CafeAsh/Pill-Pal/CAD_Files/CM4IO - KiCAD/CM4_GPIO.kicad_sch

## KiCad design CAD_Files/CM4IO - KiCAD/CM4_GPIO.kicad_sch (2025-06-23)

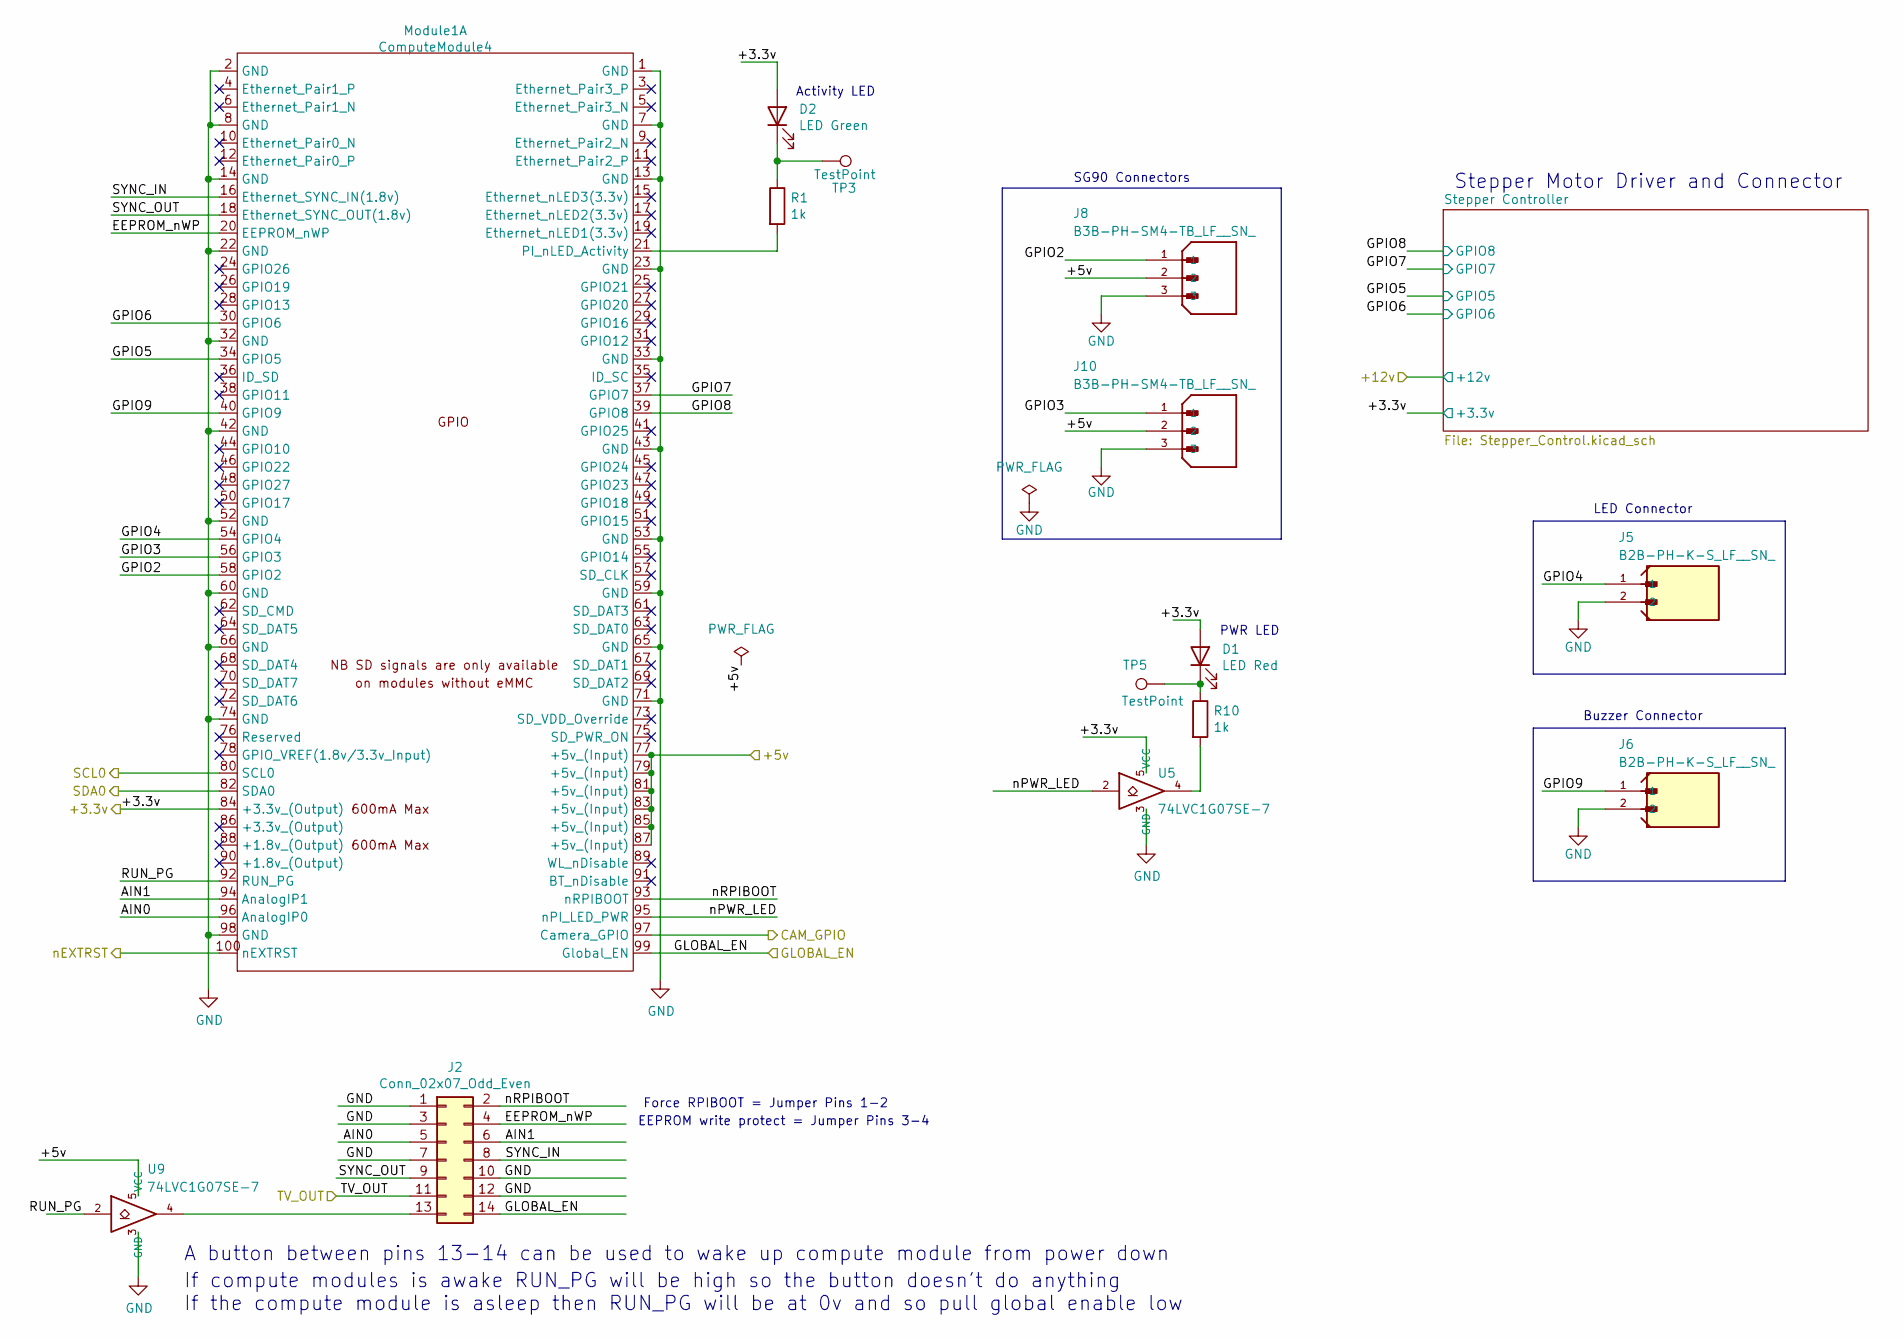
[picture p10: schematic CM4_GPIO.kicad_sch]

Parts:
D1: LED Red; LED_0603_1608Metric; Part Description Red 620nm LED Indication - Discrete 2.2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
D2: LED Green; LED_0603_1608Metric; Part Description Green 572nm LED Indication - Discrete 2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
J2: Conn_02x07_Odd_Even; PinHeader_2x07_P2.54mm_Vertical; Part Description PinHeader_2x07_P2.54mm_Vertical
J5, J6: B2B-PH-K-S_LF__SN_; JST_PH_B2B-PH-SM4-TB_1x02-1MP_P2.00mm_Vertical
J8, J10: B3B-PH-SM4-TB_LF__SN_; JST_PH_B3B-PH-SM4-TB_1x03-1MP_P2.00mm_Vertical; PARTREV N/A
Module1: ComputeModule4; Raspberry-Pi-4-Compute-Module; Part Description 100 Position Connector Receptacle, Cent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
R1, R10: 1k; R_0402_1005Metric; Part Description Resistor 1K M1005 1% 63mW
TP3, TP5: TestPoint; TestPoint_Pad_2.0x2.0mm
U5, U9: 74LVC1G07SE-7; SOT-353_SC-70-5; Part Description Buffer, Non-Inverting 1 Element 1 Bit p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

Connections:
+3.3v: D1.2 (A), D2.2 (A), Module1.84 (+3.3v_(Output)), U5.5 (VCC)
+5v: J8.2, J10.2, Module1.77 (+5v_(Input)), Module1.79 (+5v_(Input)), Module1.81 (+5v_(Input)), Module1.83 (+5v_(Input)), Module1.85 (+5v_(Input)), Module1.87 (+5v_(Input)), U9.5 (VCC)
AIN0: J2.5, Module1.96 (AnalogIP0)
AIN1: J2.6, Module1.94 (AnalogIP1)
CAM_GPIO: Module1.97 (Camera_GPIO)
EEPROM_nWP: J2.4, Module1.20 (EEPROM_nWP)
GLOBAL_EN: J2.14, Module1.99 (Global_EN)
GND: J2.1, J2.3, J2.7, J2.10, J2.12, J5.2, J6.2, J8.3, J10.3, Module1.1 (GND), Module1.2 (GND), Module1.7 (GND), Module1.8 (GND), Module1.13 (GND), Module1.14 (GND), Module1.22 (GND), Module1.23 (GND), Module1.32 (GND), Module1.33 (GND), Module1.42 (GND), Module1.43 (GND), Module1.52 (GND), Module1.53 (GND), Module1.59 (GND), Module1.60 (GND), Module1.65 (GND), Module1.66 (GND), Module1.71 (GND), Module1.74 (GND), Module1.98 (GND), U5.3 (GND), U9.3 (GND)
GPIO2: J8.1, Module1.58 (GPIO2)
GPIO3: J10.1, Module1.56 (GPIO3)
GPIO4: J5.1, Module1.54 (GPIO4)
GPIO5: Module1.34 (GPIO5)
GPIO6: Module1.30 (GPIO6)
GPIO7: Module1.37 (GPIO7)
GPIO8: Module1.39 (GPIO8)
GPIO9: J6.1, Module1.40 (GPIO9)
unnamed: D1.1 (K), R10.1, TP5.1
unnamed: D2.1 (K), R1.1, TP3.1
unnamed: J2.13, U9.4
unnamed: Module1.21 (PI_nLED_Activity), R1.2
unnamed: R10.2, U5.4
RUN_PG: Module1.92 (RUN_PG), U9.2
SCL0: Module1.80 (SCL0)
SDA0: Module1.82 (SDA0)
SYNC_IN: J2.8, Module1.16 (Ethernet_SYNC_IN(1.8v))
SYNC_OUT: J2.9, Module1.18 (Ethernet_SYNC_OUT(1.8v))
TV_OUT: J2.11
nEXTRST: Module1.100 (nEXTRST)
nPWR_LED: Module1.95 (nPI_LED_PWR), U5.2
nRPIBOOT: J2.2, Module1.93 (nRPIBOOT)

Notes on the sheet:
PWR LED
Activity LED
EEPROM write protect = Jumper Pins 3-4
LED Connector
A button between pins 13-14 can be used to wake up compute module from power down
If compute modules is awake RUN_PG will be high so the button doesn't do anything If the compute module is asleep then RUN_PG will be at 0v and so pull global enable low
Stepper Motor Driver and Connector
Force RPIBOOT = Jumper Pins 1-2
Buzzer Connector
SG90 Connectors
