CafeAsh/Pill-Pal/CAD_Files/CM4IO - KiCAD/CM4_HighSpeed.kicad_sch

## KiCad design CAD_Files/CM4IO - KiCAD/CM4_HighSpeed.kicad_sch (2025-06-23)

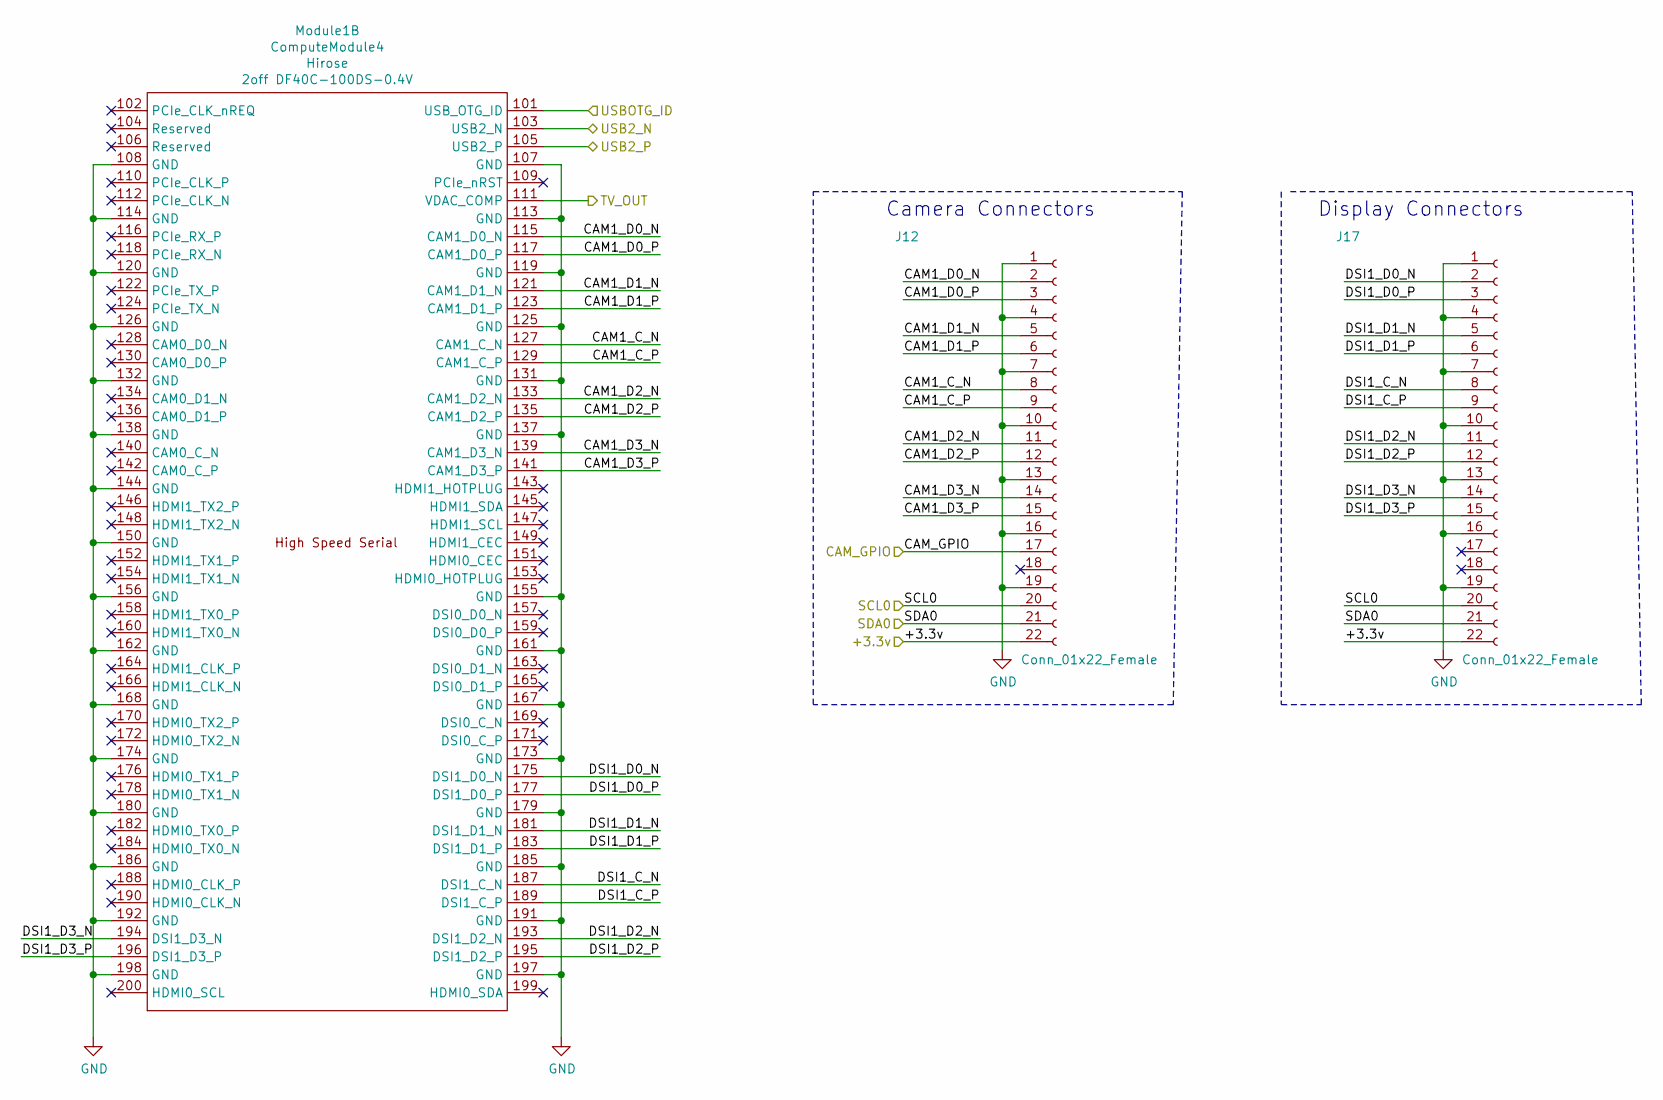
[picture p11: schematic CM4_HighSpeed.kicad_sch]

Parts:
J12, J17: Conn_01x22_Female; Hirose_FH12-22S-0.5SH_1x22-1MP_P0.50mm_Horizontal; Part Description 22 Position FFC, FPC Connector Contacts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
Module1: ComputeModule4; Raspberry-Pi-4-Compute-Module; Part Description 100 Position Connector Receptacle, Cent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

Connections:
+3.3v: J12.22, J17.22
CAM1_C_N: J12.8, Module1.127 (CAM1_C_N)
CAM1_C_P: J12.9, Module1.129 (CAM1_C_P)
CAM1_D0_N: J12.2, Module1.115 (CAM1_D0_N)
CAM1_D0_P: J12.3, Module1.117 (CAM1_D0_P)
CAM1_D1_N: J12.5, Module1.121 (CAM1_D1_N)
CAM1_D1_P: J12.6, Module1.123 (CAM1_D1_P)
CAM1_D2_N: J12.11, Module1.133 (CAM1_D2_N)
CAM1_D2_P: J12.12, Module1.135 (CAM1_D2_P)
CAM1_D3_N: J12.14, Module1.139 (CAM1_D3_N)
CAM1_D3_P: J12.15, Module1.141 (CAM1_D3_P)
CAM_GPIO: J12.17
DSI1_C_N: J17.8, Module1.187 (DSI1_C_N)
DSI1_C_P: J17.9, Module1.189 (DSI1_C_P)
DSI1_D0_N: J17.2, Module1.175 (DSI1_D0_N)
DSI1_D0_P: J17.3, Module1.177 (DSI1_D0_P)
DSI1_D1_N: J17.5, Module1.181 (DSI1_D1_N)
DSI1_D1_P: J17.6, Module1.183 (DSI1_D1_P)
DSI1_D2_N: J17.11, Module1.193 (DSI1_D2_N)
DSI1_D2_P: J17.12, Module1.195 (DSI1_D2_P)
DSI1_D3_N: J17.14, Module1.194 (DSI1_D3_N)
DSI1_D3_P: J17.15, Module1.196 (DSI1_D3_P)
GND: J12.1, J12.4, J12.7, J12.10, J12.13, J12.16, J12.19, J17.1, J17.4, J17.7, J17.10, J17.13, J17.16, J17.19, Module1.107 (GND), Module1.108 (GND), Module1.113 (GND), Module1.114 (GND), Module1.119 (GND), Module1.120 (GND), Module1.125 (GND), Module1.126 (GND), Module1.131 (GND), Module1.132 (GND), Module1.137 (GND), Module1.138 (GND), Module1.144 (GND), Module1.150 (GND), Module1.155 (GND), Module1.156 (GND), Module1.161 (GND), Module1.162 (GND), Module1.167 (GND), Module1.168 (GND), Module1.173 (GND), Module1.174 (GND), Module1.179 (GND), Module1.180 (GND), Module1.185 (GND), Module1.186 (GND), Module1.191 (GND), Module1.192 (GND), Module1.197 (GND), Module1.198 (GND)
SCL0: J12.20, J17.20
SDA0: J12.21, J17.21
TV_OUT: Module1.111 (VDAC_COMP)
USB2_N: Module1.103 (USB2_N)
USB2_P: Module1.105 (USB2_P)
USBOTG_ID: Module1.101 (USB_OTG_ID)

Notes on the sheet:
Camera Connectors
Display Connectors
