CafeAsh/Pill-Pal/CAD_Files/CM4IO - KiCAD/PCIe.kicad_sch

## KiCad design CAD_Files/CM4IO - KiCAD/PCIe.kicad_sch (2025-06-23)

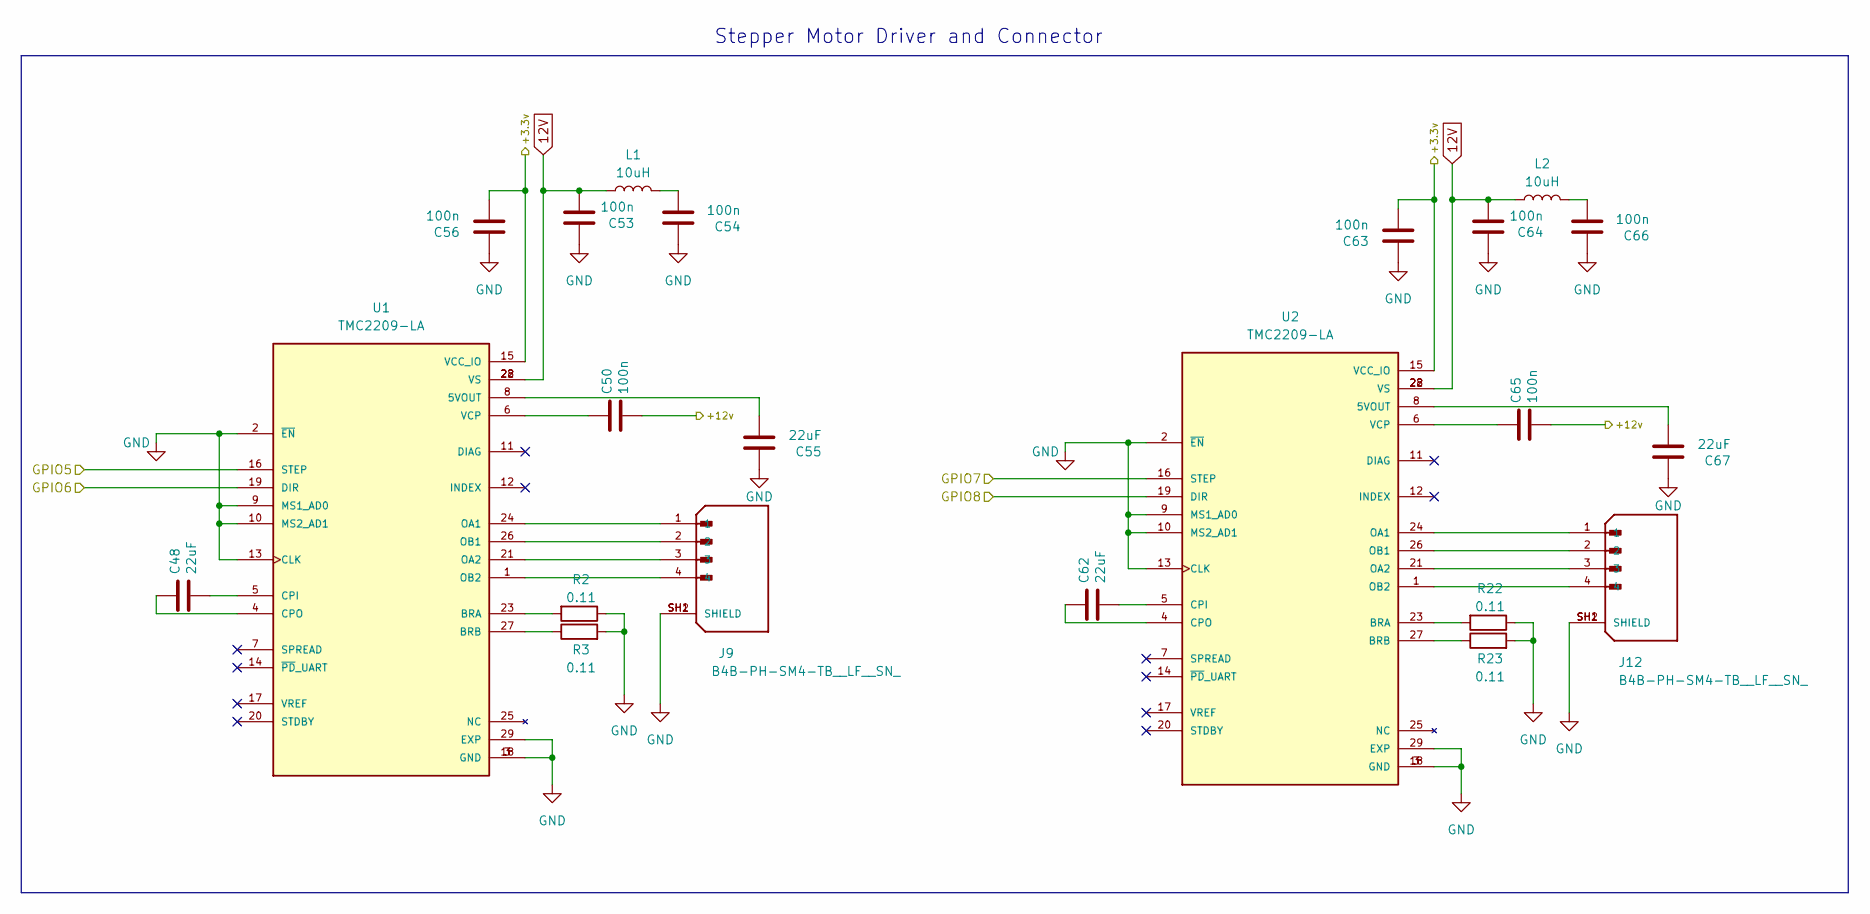
[picture p12: schematic PCIe.kicad_sch]

Parts:
C48, C55, C62, C67: 22uF; C_0402_1005Metric; Part Description 0.1uF 10% 16V Ceramic Capacitor X7R 040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
C50, C53, C54, C56, C63, C64, C65, C66: 100n; C_0402_1005Metric; Part Description 0.1uF 10% 16V Ceramic Capacitor X7R 040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
J9, J12: B4B-PH-SM4-TB__LF__SN_; JST_B4B-PH-SM4-TB__LF__SN_; PARTREV N/A
L1, L2: 10uH
R2, R3, R22, R23: 0.11
U1, U2: TMC2209-LA; QFN50P500X500X90-29N; PARTREV 1.08

Connections:
12V: C53.2, C64.2, L1.1, L2.1, U1.22 (VS), U1.28 (VS), U2.22 (VS), U2.28 (VS)
+3.3v: C56.2, C63.2, U1.15 (VCC_IO), U2.15 (VCC_IO)
+12v: C50.2, C65.2
GND: C53.1, C54.1, C55.1, C56.1, C63.1, C64.1, C66.1, C67.1, J9.SH1 (SHIELD), J9.SH2 (SHIELD), J12.SH1 (SHIELD), J12.SH2 (SHIELD), R2.1, R3.2, R22.1, R23.2, U1.2 (~EN), U1.3 (GND), U1.9 (MS1_AD0), U1.10 (MS2_AD1), U1.13 (CLK), U1.18 (GND), U1.29 (EXP), U2.2 (~EN), U2.3 (GND), U2.9 (MS1_AD0), U2.10 (MS2_AD1), U2.13 (CLK), U2.18 (GND), U2.29 (EXP)
GPIO5: U1.16 (STEP)
GPIO6: U1.19 (DIR)
GPIO7: U2.16 (STEP)
GPIO8: U2.19 (DIR)
unnamed: C48.1, U1.4 (CPO)
unnamed: C48.2, U1.5 (CPI)
unnamed: C50.1, U1.6 (VCP)
unnamed: C54.2, L1.2
unnamed: C55.2, U1.8 (5VOUT)
unnamed: C62.1, U2.4 (CPO)
unnamed: C62.2, U2.5 (CPI)
unnamed: C65.1, U2.6 (VCP)
unnamed: C66.2, L2.2
unnamed: C67.2, U2.8 (5VOUT)
unnamed: J9.1, U1.24 (OA1)
unnamed: J9.2, U1.26 (OB1)
unnamed: J9.3, U1.21 (OA2)
unnamed: J9.4, U1.1 (OB2)
unnamed: J12.1, U2.24 (OA1)
unnamed: J12.2, U2.26 (OB1)
unnamed: J12.3, U2.21 (OA2)
unnamed: J12.4, U2.1 (OB2)
unnamed: R2.2, U1.23 (BRA)
unnamed: R3.1, U1.27 (BRB)
unnamed: R22.2, U2.23 (BRA)
unnamed: R23.1, U2.27 (BRB)

Notes on the sheet:
Stepper Motor Driver and Connector
