CafeAsh/Pill-Pal/CAD_Files/CM4IO - KiCAD/PSUs.kicad_sch

## KiCad design CAD_Files/CM4IO - KiCAD/PSUs.kicad_sch (2025-06-23)

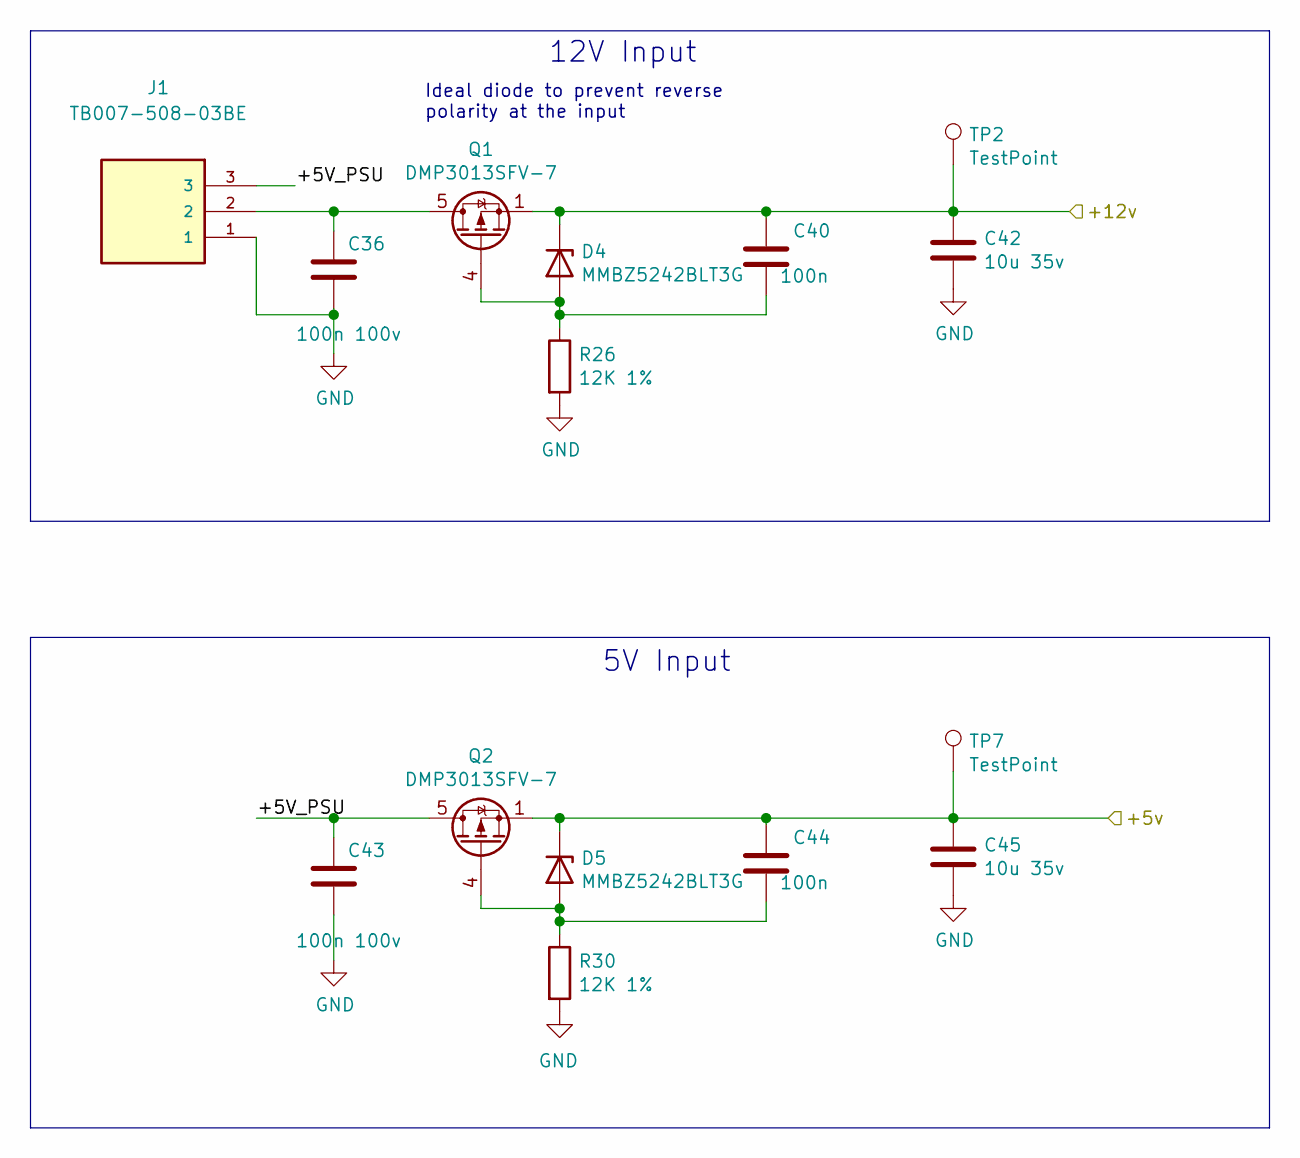
[picture p13: schematic PSUs.kicad_sch]

Parts:
C36, C43: 100n 100v; C_0402_1005Metric; Part Description 0.1uF 10% 100V Ceramic Capacitor X5R 04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
C40, C44: 100n; C_0402_1005Metric; Part Description 0.1uF 10% 16V Ceramic Capacitor X7R 040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
C42, C45: 10u 35v; C_0805_2012Metric; Part Description 10uF 10% or 20% 35V Ceramic Capacitor X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
D4, D5: MMBZ5242BLT3G; D_0201_0603Metric; Part Description Zener Diode 12V 225mW 5% Surface Mount 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
J1: TB007-508-03BE; CUI_TB007-508-03BE
Q1, Q2: DMP3013SFV-7; Diodes_PowerDI3333-8; Part Description DMP3013SFV-7 - Power MOSFET, P Channel,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
R26, R30: 12K 1%; R_0402_1005Metric; Part Description Resistor 12K M1005 1% 63mW
TP2, TP7: TestPoint; TestPoint_Pad_2.0x2.0mm

Connections:
+5V_PSU: C43.1, J1.3, Q2.5 (D)
+5v: C44.1, C45.1, D5.1 (K), Q2.1 (S), Q2.2 (S), Q2.3 (S), TP7.1
+12v: C40.1, C42.1, D4.1 (K), Q1.1 (S), Q1.2 (S), Q1.3 (S), TP2.1
GND: C36.2, C42.2, C43.2, C45.2, J1.1, R26.2, R30.2
unnamed: C36.1, J1.2, Q1.5 (D)
unnamed: C40.2, D4.2 (A), Q1.4 (G), R26.1
unnamed: C44.2, D5.2 (A), Q2.4 (G), R30.1

Notes on the sheet:
12V Input
5V Input
Ideal diode to prevent reverse polarity at the input
