CafeAsh/Pill-Pal/CAD_Files/CM4IO - KiCAD/RTC.kicad_sch

## KiCad design CAD_Files/CM4IO - KiCAD/RTC.kicad_sch (2025-06-23)

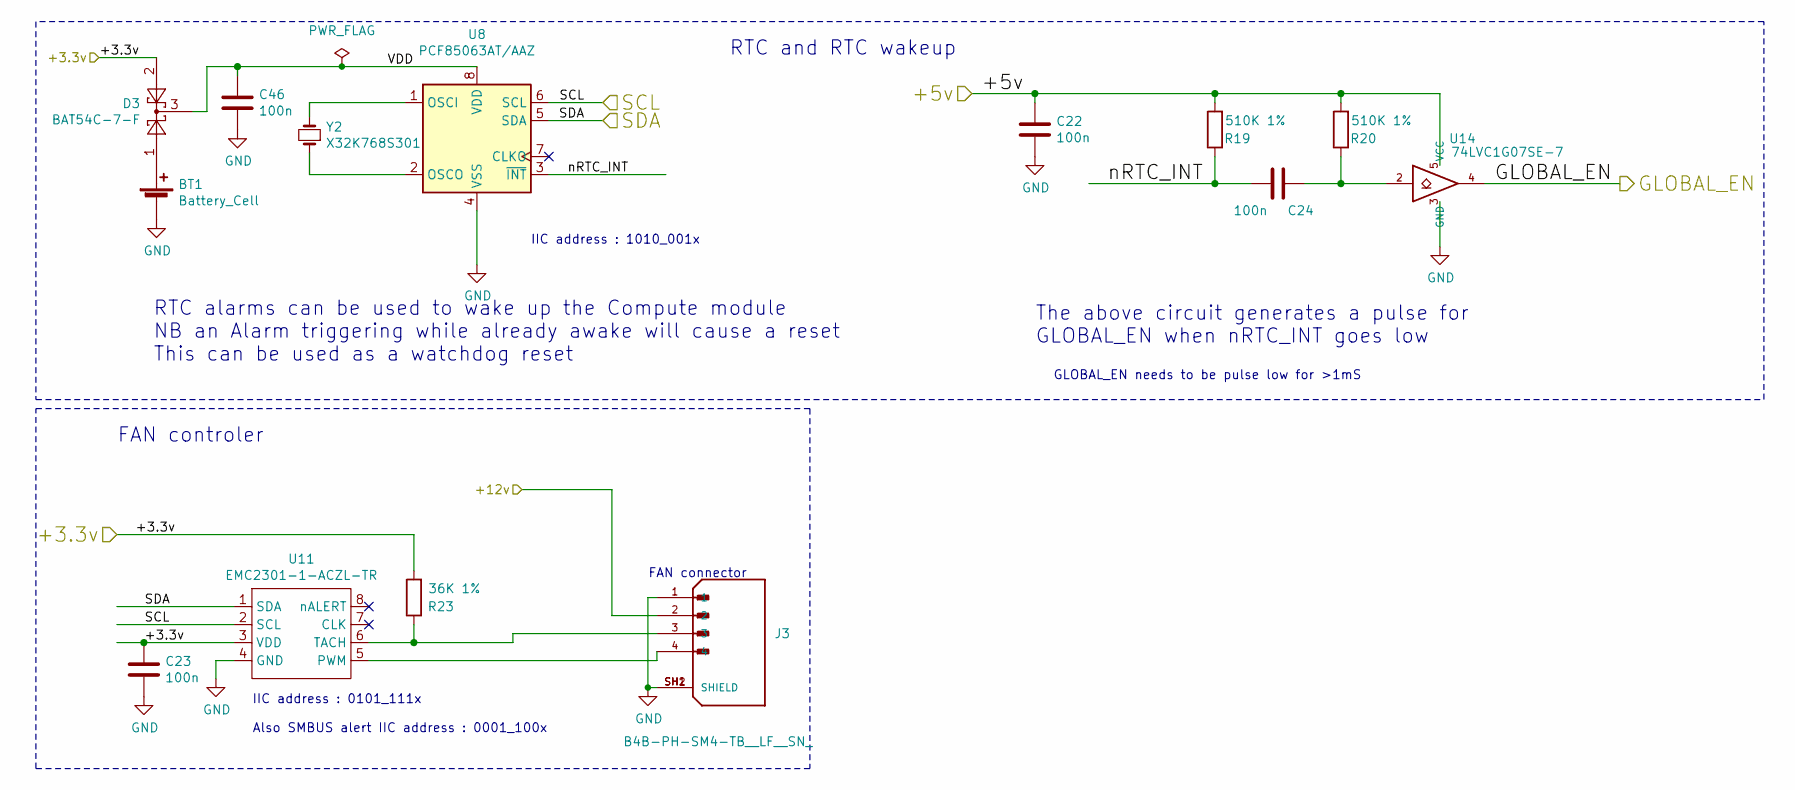
[picture p14: schematic RTC.kicad_sch]

Parts:
BT1: Battery_Cell; BatteryHolder_Keystone_3034_1x20mm; Part Description Battery Retainer Coin, 20.0mm 1 Cell SM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
C22, C23, C24, C46: 100n; C_0402_1005Metric; Part Description 0.1uF 10% 16V Ceramic Capacitor X7R 040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
D3: BAT54C-7-F; SOT-23; Part Description Diode Array 1 Pair Common Cathode Schot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
J3: B4B-PH-SM4-TB__LF__SN_; JST_B4B-PH-SM4-TB__LF__SN_; PARTREV N/A
R19, R20: 510K 1%; R_0402_1005Metric; Part Description Resistor 510K M1005 1% 63mW
R23: 36K 1%; R_0402_1005Metric; Part Description Resistor 36K M1005 1% 63mW
U8: PCF85063AT/AAZ; SOIC-8_3.9x4.9mm_P1.27mm; Part Description Real Time Clock (RTC) IC Clock/Calendar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
U11: EMC2301-1-ACZL-TR; MSOP-8_3x3mm_P0.65mm; Part Description Motor Driver PWM 8-MSOP
U14: 74LVC1G07SE-7; SOT-353_SC-70-5; Part Description Buffer, Non-Inverting 1 Element 1 Bit p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
Y2: X32K768S301; Crystal_SMD_3215-2Pin_3.2x1.5mm; Part Description Crystal 32.768KHz 7pF 20pmm

Connections:
+3.3v: C23.1, D3.2, R23.2, U11.3 (VDD)
+5v: C22.1, R19.2, R20.2, U14.5 (VCC)
+12v: J3.2
GLOBAL_EN: U14.4
GND: BT1.2 (-), C22.2, C23.2, C46.2, J3.1, J3.SH1 (SHIELD), J3.SH2 (SHIELD), U8.4 (VSS), U11.4 (GND), U14.3 (GND)
unnamed: BT1.1 (+), D3.1
unnamed: C24.1, R20.1, U14.2
unnamed: J3.3, R23.1, U11.6 (TACH)
unnamed: J3.4, U11.5 (PWM)
unnamed: U8.1 (OSCI), Y2.2
unnamed: U8.2 (OSCO), Y2.1
SCL: U8.6 (SCL), U11.2 (SCL)
SDA: U8.5 (SDA), U11.1 (SDA)
VDD: C46.1, D3.3, U8.8 (VDD)
nRTC_INT: C24.2, R19.1, U8.3 (~INT)

Notes on the sheet:
FAN controler
RTC alarms can be used to wake up the Compute module NB an Alarm triggering while already awake will cause a reset This can be used as a watchdog reset
RTC and RTC wakeup
IIC address : 1010_001x
IIC address : 0101_111x
Also SMBUS alert IIC address : 0001_100x
GLOBAL_EN needs to be pulse low for >1mS
FAN connector
The above circuit generates a pulse for GLOBAL_EN when nRTC_INT goes low
