CafeAsh/Pill-Pal/CAD_Files/CM4IO - KiCAD/Stepper_Control.kicad_sch

## KiCad design CAD_Files/CM4IO - KiCAD/Stepper_Control.kicad_sch (2025-06-23)

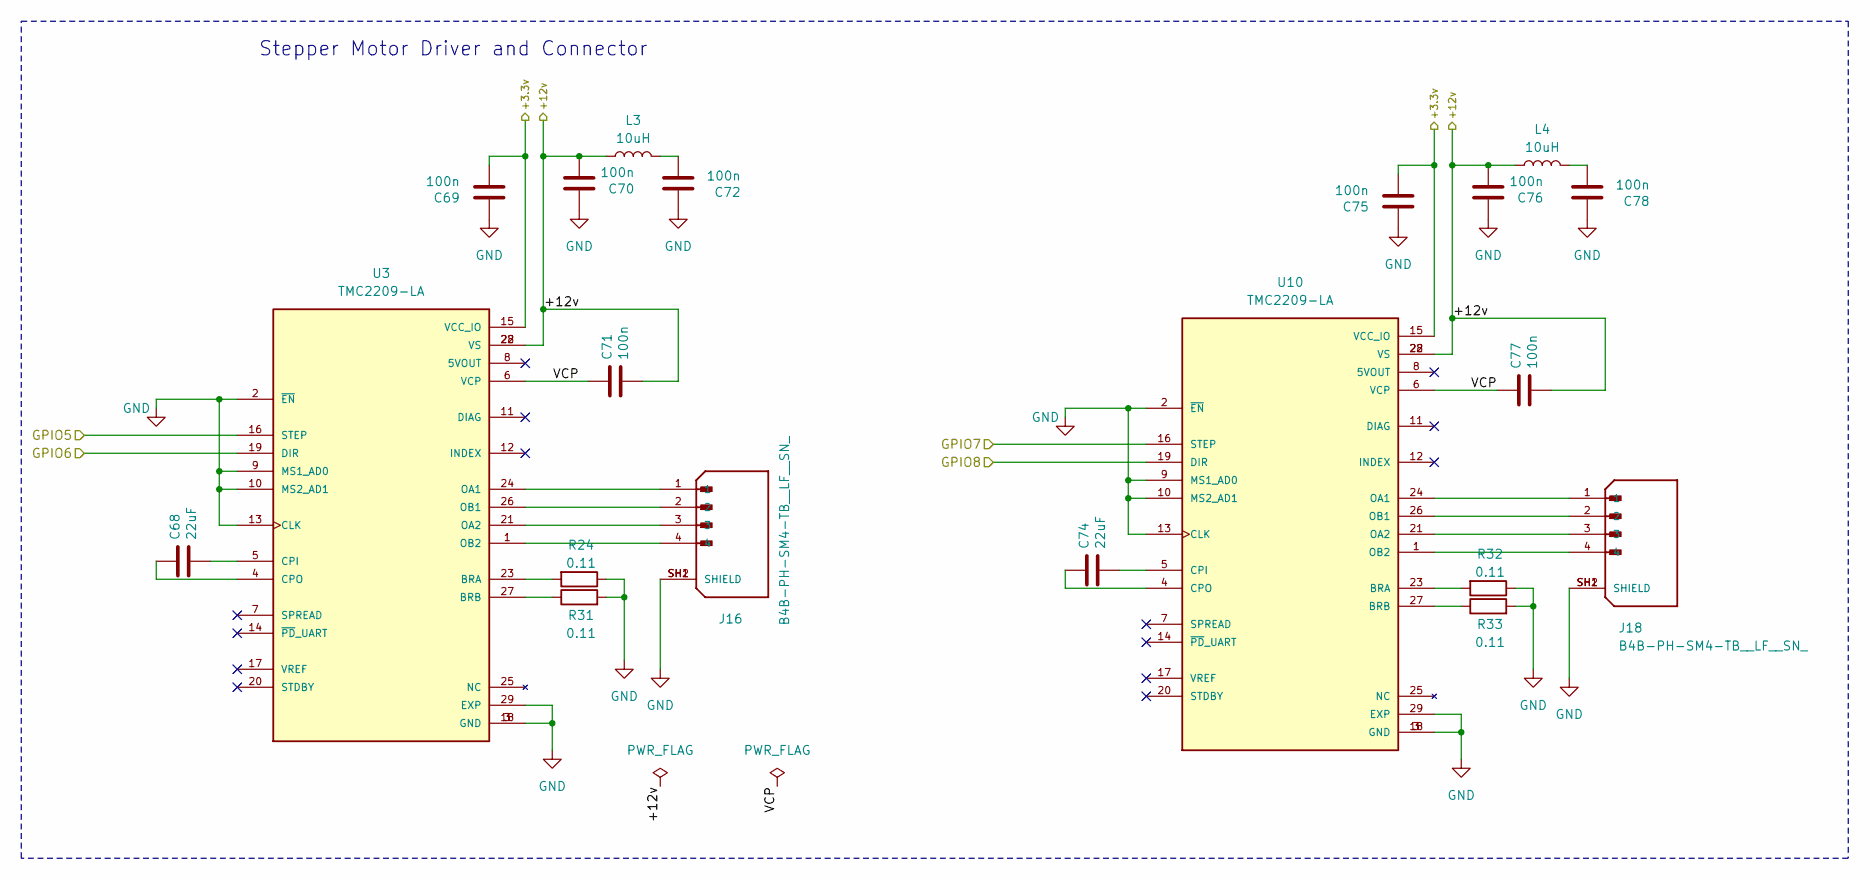
[picture p15: schematic Stepper_Control.kicad_sch]

Parts:
C68, C74: 22uF; C_0402_1005Metric; Part Description 0.1uF 10% 16V Ceramic Capacitor X7R 040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
C69, C70, C71, C72, C75, C76, C77, C78: 100n; C_0402_1005Metric; Part Description 0.1uF 10% 16V Ceramic Capacitor X7R 040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
J16, J18: B4B-PH-SM4-TB__LF__SN_; JST_PH_B4B-PH-SM4-TB_1x04-1MP_P2.00mm_Vertical; PARTREV N/A
L3, L4: 10uH; L_0201_0603Metric
R24, R31, R32, R33: 0.11; R_0402_1005Metric
U3, U10: TMC2209-LA; QFN50P500X500X90-29N; PARTREV 1.08

Connections:
+3.3v: C69.2, C75.2, U3.15 (VCC_IO), U10.15 (VCC_IO)
+12v: C70.2, C71.2, C76.2, C77.2, L3.1, L4.1, U3.22 (VS), U3.28 (VS), U10.22 (VS), U10.28 (VS)
GND: C69.1, C70.1, C72.1, C75.1, C76.1, C78.1, J16.SH1 (SHIELD), J16.SH2 (SHIELD), J18.SH1 (SHIELD), J18.SH2 (SHIELD), R24.1, R31.2, R32.1, R33.2, U3.2 (~EN), U3.3 (GND), U3.9 (MS1_AD0), U3.10 (MS2_AD1), U3.13 (CLK), U3.18 (GND), U3.29 (EXP), U10.2 (~EN), U10.3 (GND), U10.9 (MS1_AD0), U10.10 (MS2_AD1), U10.13 (CLK), U10.18 (GND), U10.29 (EXP)
GPIO5: U3.16 (STEP)
GPIO6: U3.19 (DIR)
GPIO7: U10.16 (STEP)
GPIO8: U10.19 (DIR)
unnamed: C68.1, U3.4 (CPO)
unnamed: C68.2, U3.5 (CPI)
unnamed: C72.2, L3.2
unnamed: C74.1, U10.4 (CPO)
unnamed: C74.2, U10.5 (CPI)
unnamed: C78.2, L4.2
unnamed: J16.1, U3.24 (OA1)
unnamed: J16.2, U3.26 (OB1)
unnamed: J16.3, U3.21 (OA2)
unnamed: J16.4, U3.1 (OB2)
unnamed: J18.1, U10.24 (OA1)
unnamed: J18.2, U10.26 (OB1)
unnamed: J18.3, U10.21 (OA2)
unnamed: J18.4, U10.1 (OB2)
unnamed: R24.2, U3.23 (BRA)
unnamed: R31.1, U3.27 (BRB)
unnamed: R32.2, U10.23 (BRA)
unnamed: R33.1, U10.27 (BRB)
VCP: C71.1, C77.1, U3.6 (VCP), U10.6 (VCP)

Notes on the sheet:
Stepper Motor Driver and Connector
