CafeAsh/Pill-Pal/CAD_Files/CM4IO - KiCAD/USB2-HUB.kicad_sch

## KiCad design CAD_Files/CM4IO - KiCAD/USB2-HUB.kicad_sch (2025-06-23)

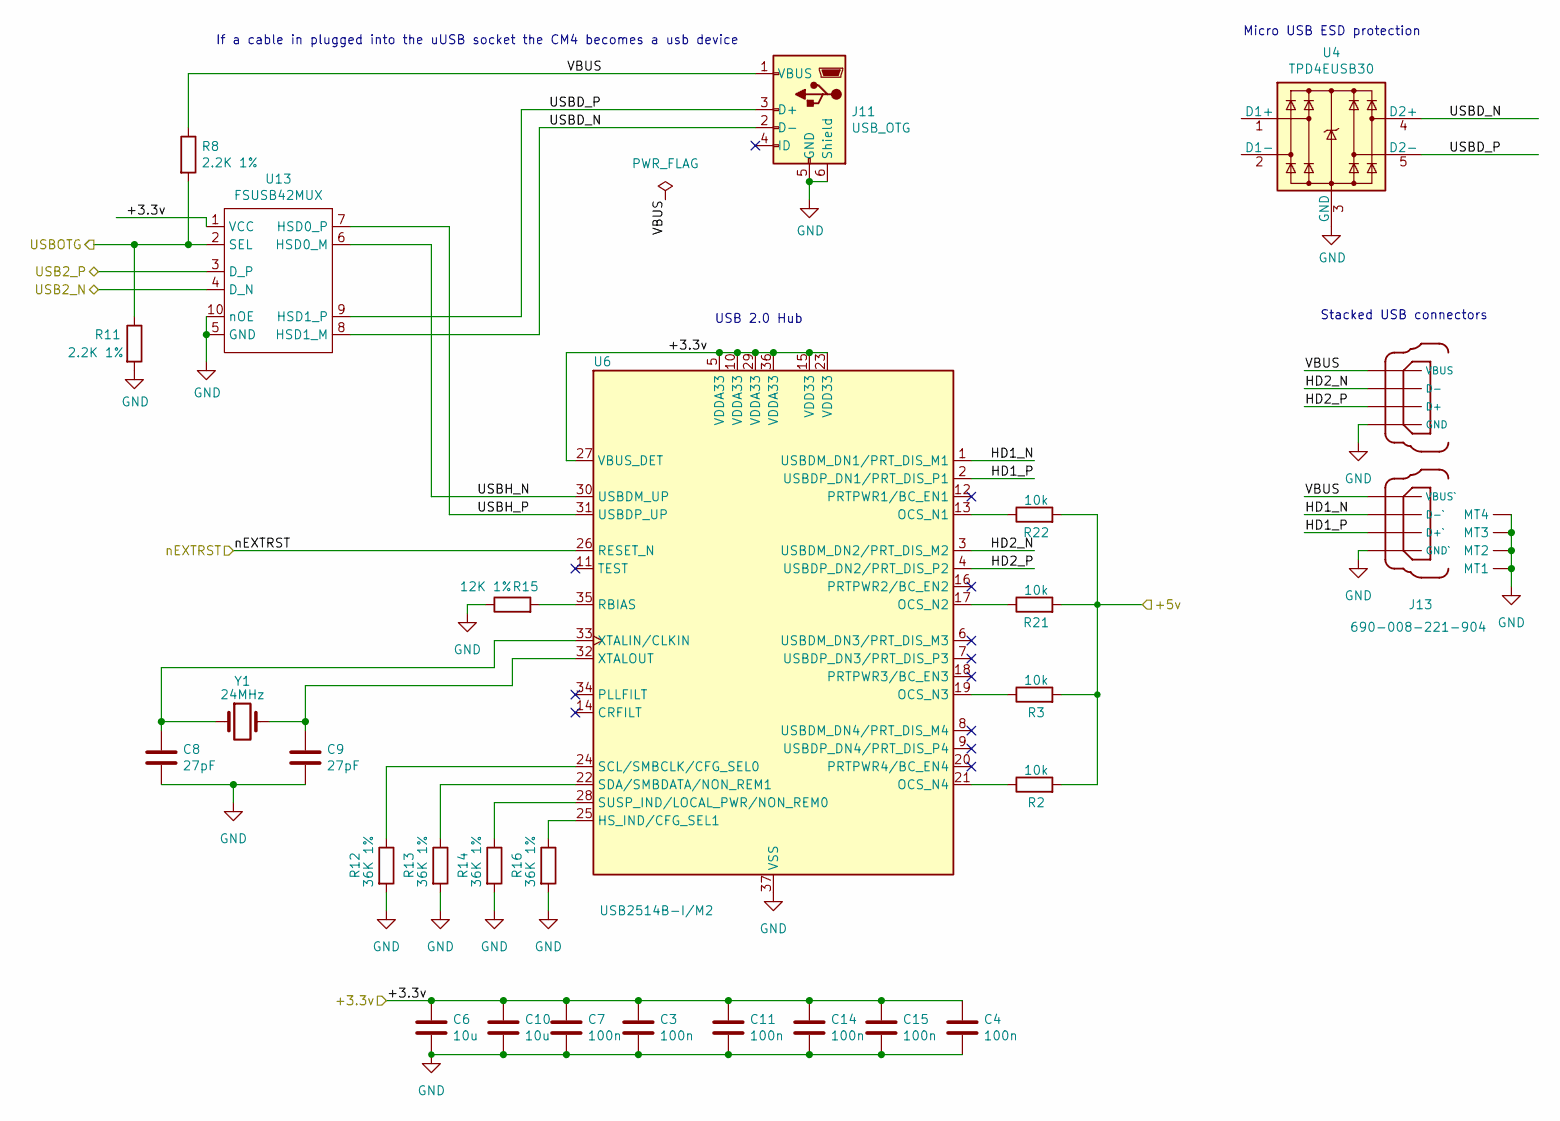
[picture p16: schematic USB2-HUB.kicad_sch]

Parts:
C3, C4, C7, C11, C14, C15: 100n; C_0402_1005Metric; Part Description 0.1uF 10% 16V Ceramic Capacitor X7R 040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
C6, C10: 10u; C_0805_2012Metric; Part Description 10uF 10% 10V Ceramic Capacitor X7R 0805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
C8, C9: 27pF; C_0402_1005Metric; Part Description 27pF 5% 50V Ceramic Capacitor C0G, NP0 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
J11: USB_OTG; USB_Micro-B_EDAC_UCON00686; Part Description USB - micro B USB 2.0 Receptacle Connec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
J13: 690-008-221-904; MOLEX_USB_67298-4090; Part Description USB-A (USB TYPE-A), Stacked Receptacle 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
R2, R3, R21, R22: 10k; R_0402_1005Metric
R8, R11: 2.2K 1%; R_0402_1005Metric; Part Description Resistor 2.2K M1005 1% 63mW
R12, R13, R14, R16: 36K 1%; R_0402_1005Metric; Part Description Resistor 36K M1005 1% 63mW
R15: 12K 1%; R_0402_1005Metric; Part Description Resistor 12K M1005 1% 63mW
U4: TPD4EUSB30; USON-10_2.5x1.0mm_P0.5mm; Part Description Quad TVS diode for high speed signals (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
U6: USB2514B-I/M2; QFN-36-1EP_6x6mm_P0.5mm_EP3.7x3.7mm; Part Description USB Hub Controller USB Interface 36-SQF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
U13: FSUSB42MUX; MSOP-10_3x3mm_P0.5mm; Part Description USB Switch IC 1 Channel 10-MSOP
Y1: 24MHz; Crystal_SMD_HC49-SD; Part Description 24MHz Crystal 18pf 30ppm 30ppm

Connections:
+3.3v: C3.1, C4.1, C6.1, C7.1, C10.1, C11.1, C14.1, C15.1, U6.5 (VDDA33), U6.10 (VDDA33), U6.15 (VDD33), U6.23 (VDD33), U6.27 (VBUS_DET), U6.29 (VDDA33), U6.36 (VDDA33), U13.1 (VCC)
+5v: R2.2, R3.2, R21.2, R22.2
GND: C3.2, C4.2, C6.2, C7.2, C8.2, C9.2, C10.2, C11.2, C14.2, C15.2, J11.5 (GND), J11.6 (Shield), J13.4 (GND`), J13.8 (GND), J13.MT1, J13.MT2, J13.MT3, J13.MT4, R11.2, R12.2, R13.2, R14.2, R15.1, R16.2, U4.3 (GND), U4.8 (GND), U6.37 (VSS), U13.5 (GND), U13.10 (nOE)
HD1_N: J13.2 (D-`), U6.1 (USBDM_DN1/PRT_DIS_M1)
HD1_P: J13.3 (D+`), U6.2 (USBDP_DN1/PRT_DIS_P1)
HD2_N: J13.6 (D-), U6.3 (USBDM_DN2/PRT_DIS_M2)
HD2_P: J13.7 (D+), U6.4 (USBDP_DN2/PRT_DIS_P2)
unnamed: C8.1, U6.33 (XTALIN/CLKIN), Y1.1
unnamed: C9.1, U6.32 (XTALOUT), Y1.2
unnamed: R2.1, U6.21 (OCS_N4)
unnamed: R3.1, U6.19 (OCS_N3)
unnamed: R12.1, U6.24 (SCL/SMBCLK/CFG_SEL0)
unnamed: R13.1, U6.22 (SDA/SMBDATA/NON_REM1)
unnamed: R14.1, U6.28 (SUSP_IND/LOCAL_PWR/NON_REM0)
unnamed: R15.2, U6.35 (RBIAS)
unnamed: R16.1, U6.25 (HS_IND/CFG_SEL1)
unnamed: R21.1, U6.17 (OCS_N2)
unnamed: R22.1, U6.13 (OCS_N1)
unnamed: U4.1 (D1+), U4.10
unnamed: U4.2 (D1-), U4.9
USB2_N: U13.4 (D_N)
USB2_P: U13.3 (D_P)
USBD_N: J11.2 (D-), U4.4 (D2+), U4.7, U13.8 (HSD1_M)
USBD_P: J11.3 (D+), U4.5 (D2-), U4.6, U13.9 (HSD1_P)
USBH_N: U6.30 (USBDM_UP), U13.6 (HSD0_M)
USBH_P: U6.31 (USBDP_UP), U13.7 (HSD0_P)
USBOTG: R8.2, R11.1, U13.2 (SEL)
VBUS: J11.1 (VBUS), J13.1 (VBUS`), J13.5 (VBUS), R8.1
nEXTRST: U6.26 (RESET_N)

Notes on the sheet:
USB 2.0 Hub
If a cable in plugged into the uUSB socket the CM4 becomes a usb device
Micro USB ESD protection
Stacked USB connectors
